TeknoBeek/KTS_Open_Source/Etiketler_PGN/001.png

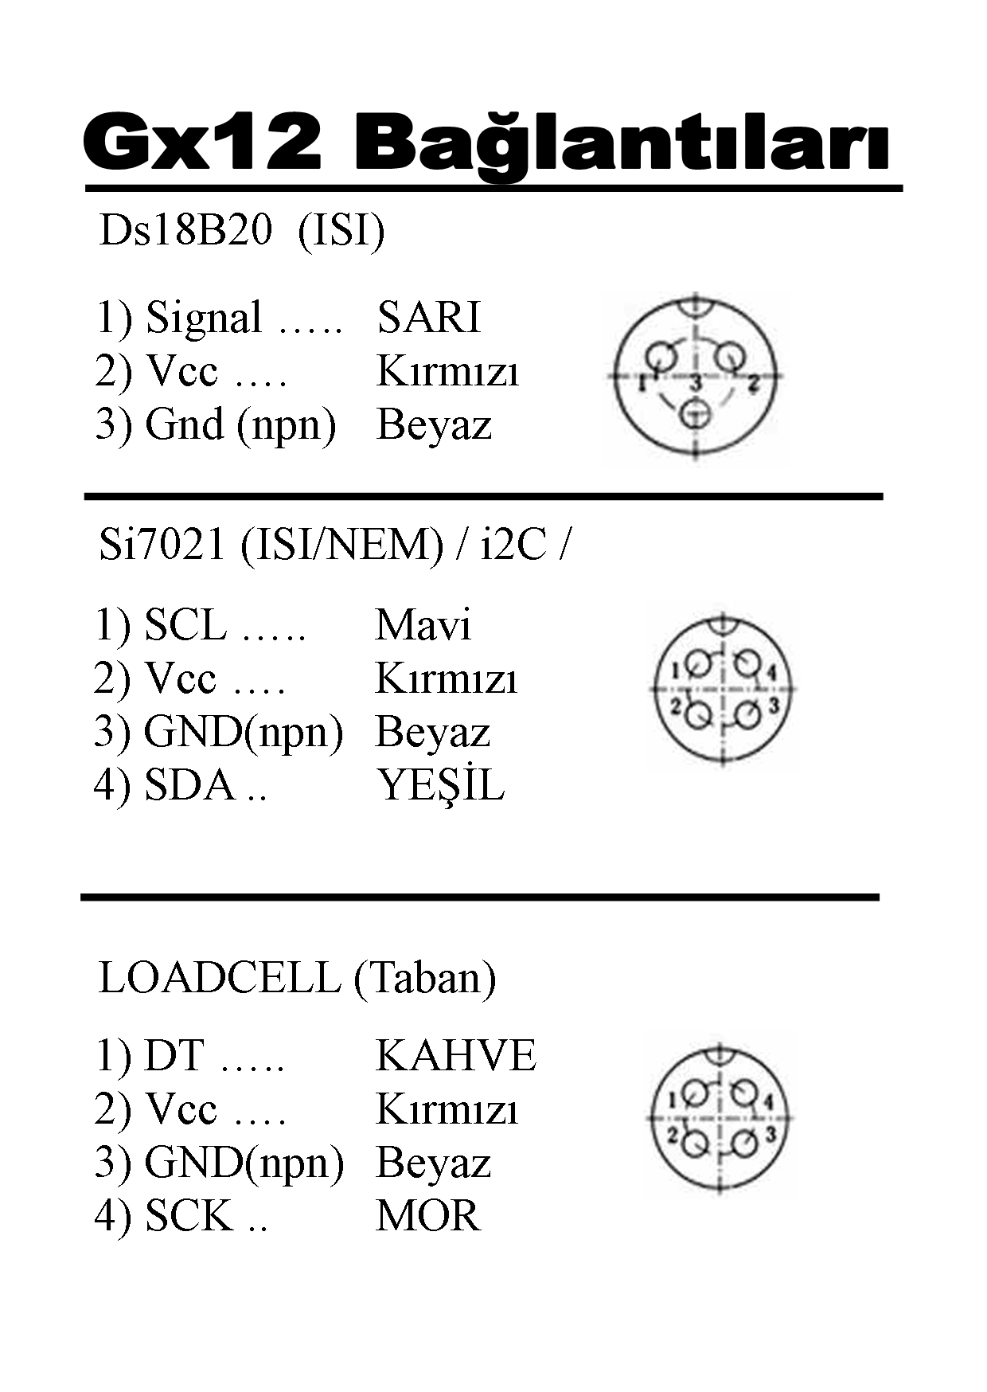
Etiketler_PGN/001.png
