TeknoBeek/KTS_Open_Source/Etiketler_PGN/002.png

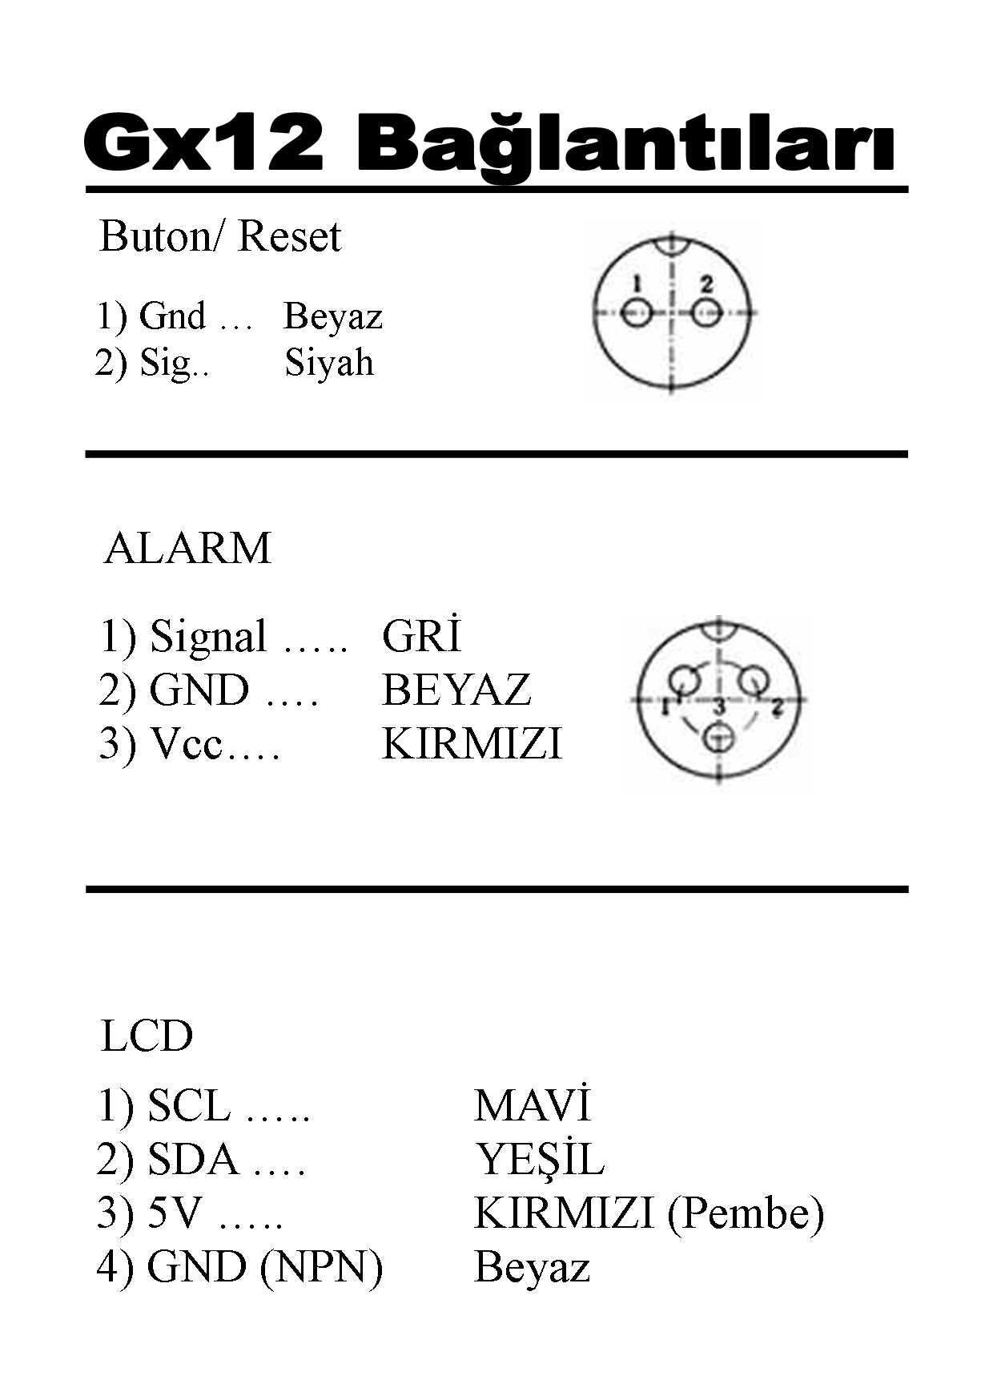
Etiketler_PGN/002.png
