TeknoBeek/KTS_Open_Source/Etiketler_PGN/003.png

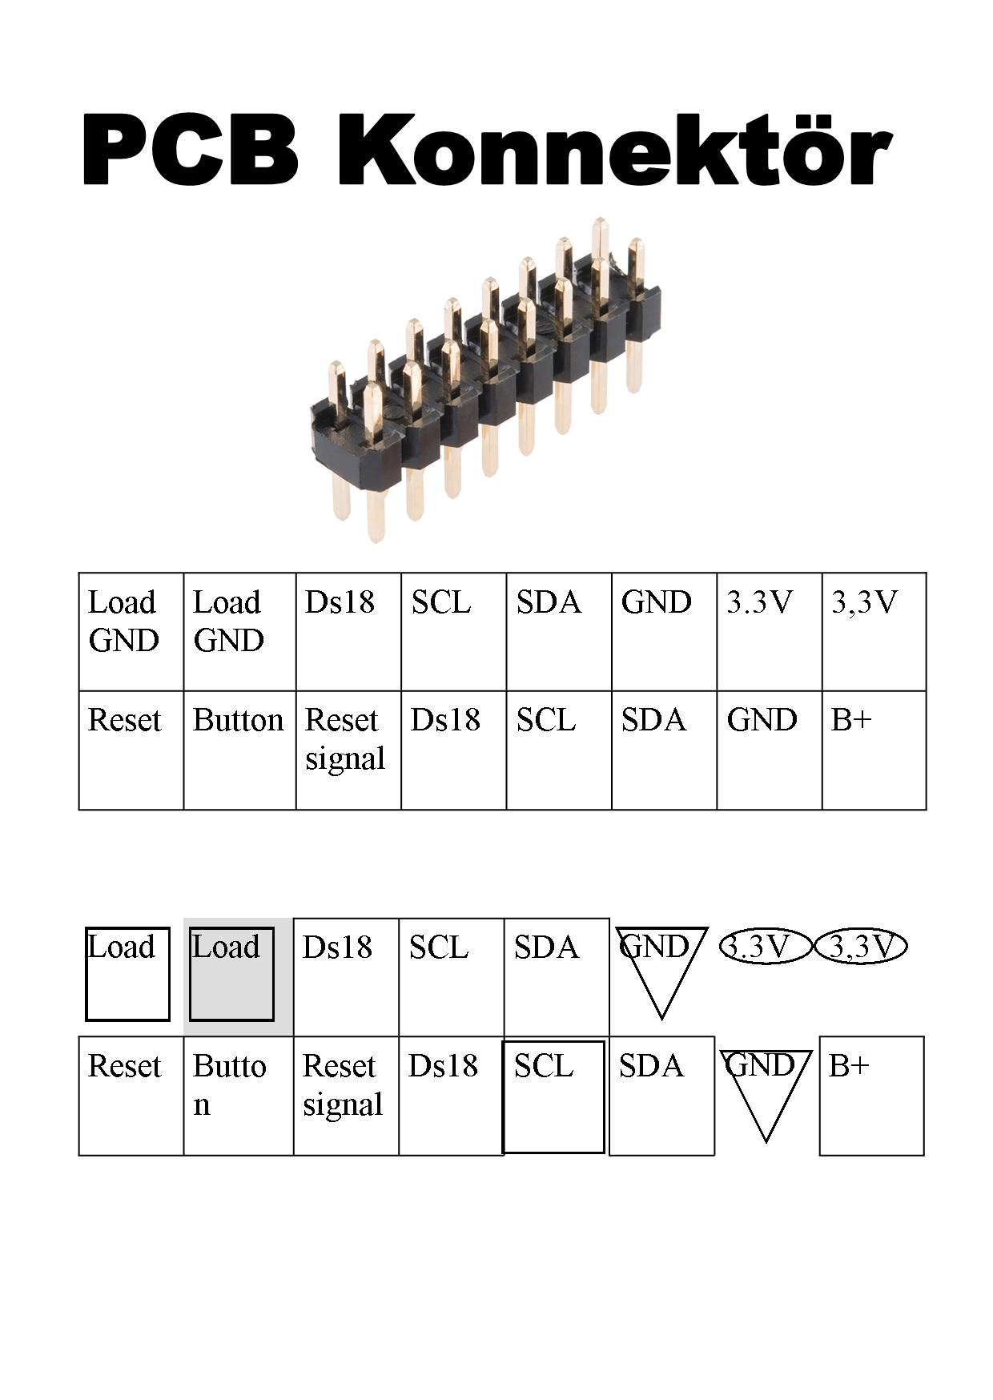
Etiketler_PGN/003.png
