TeknoBeek/KTS_Open_Source/Etiketler_PGN/004.png

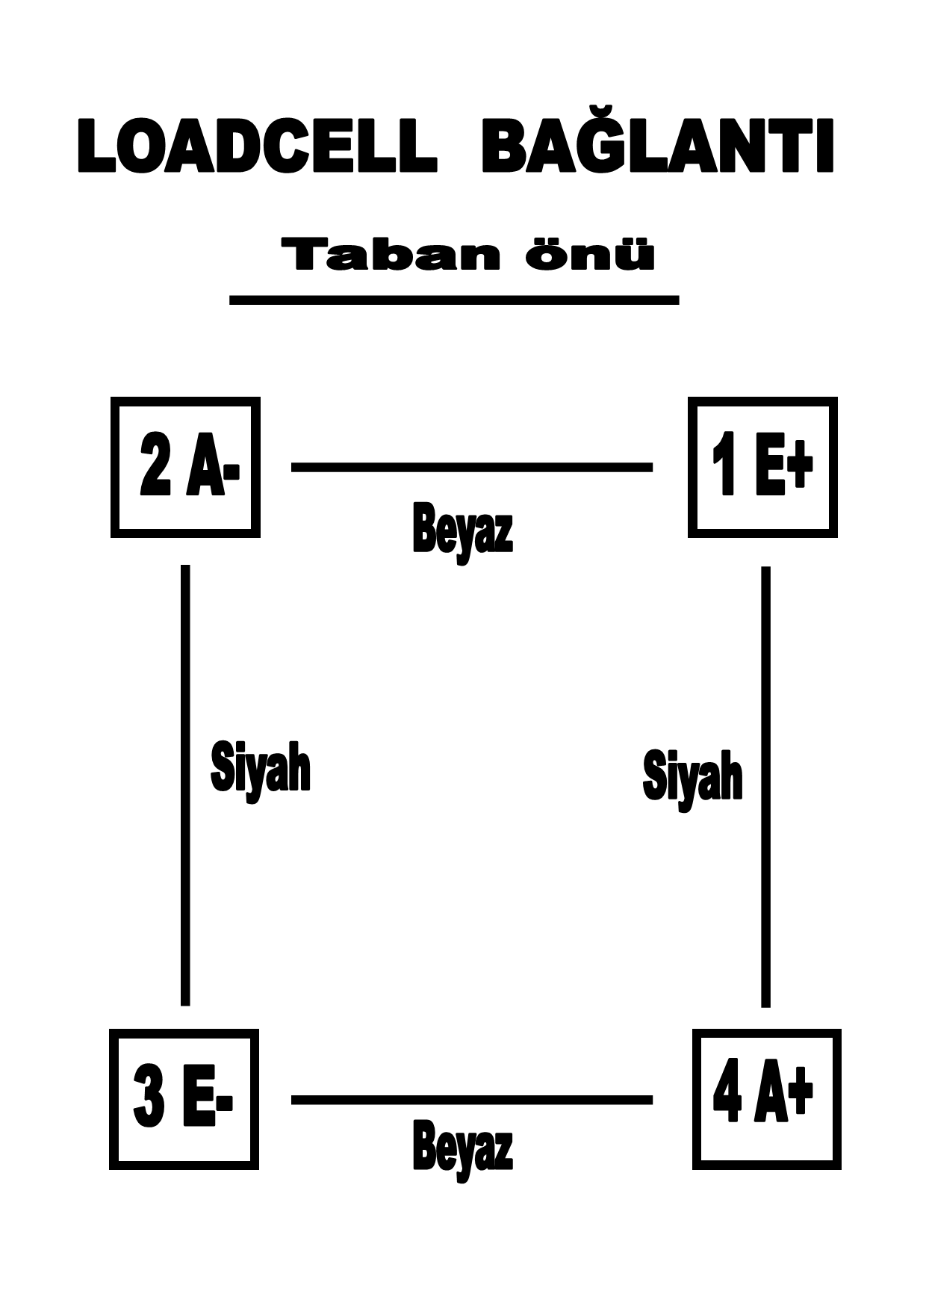
Etiketler_PGN/004.png
