TeknoBeek/KTS_Open_Source/Etiketler_PGN/005.png

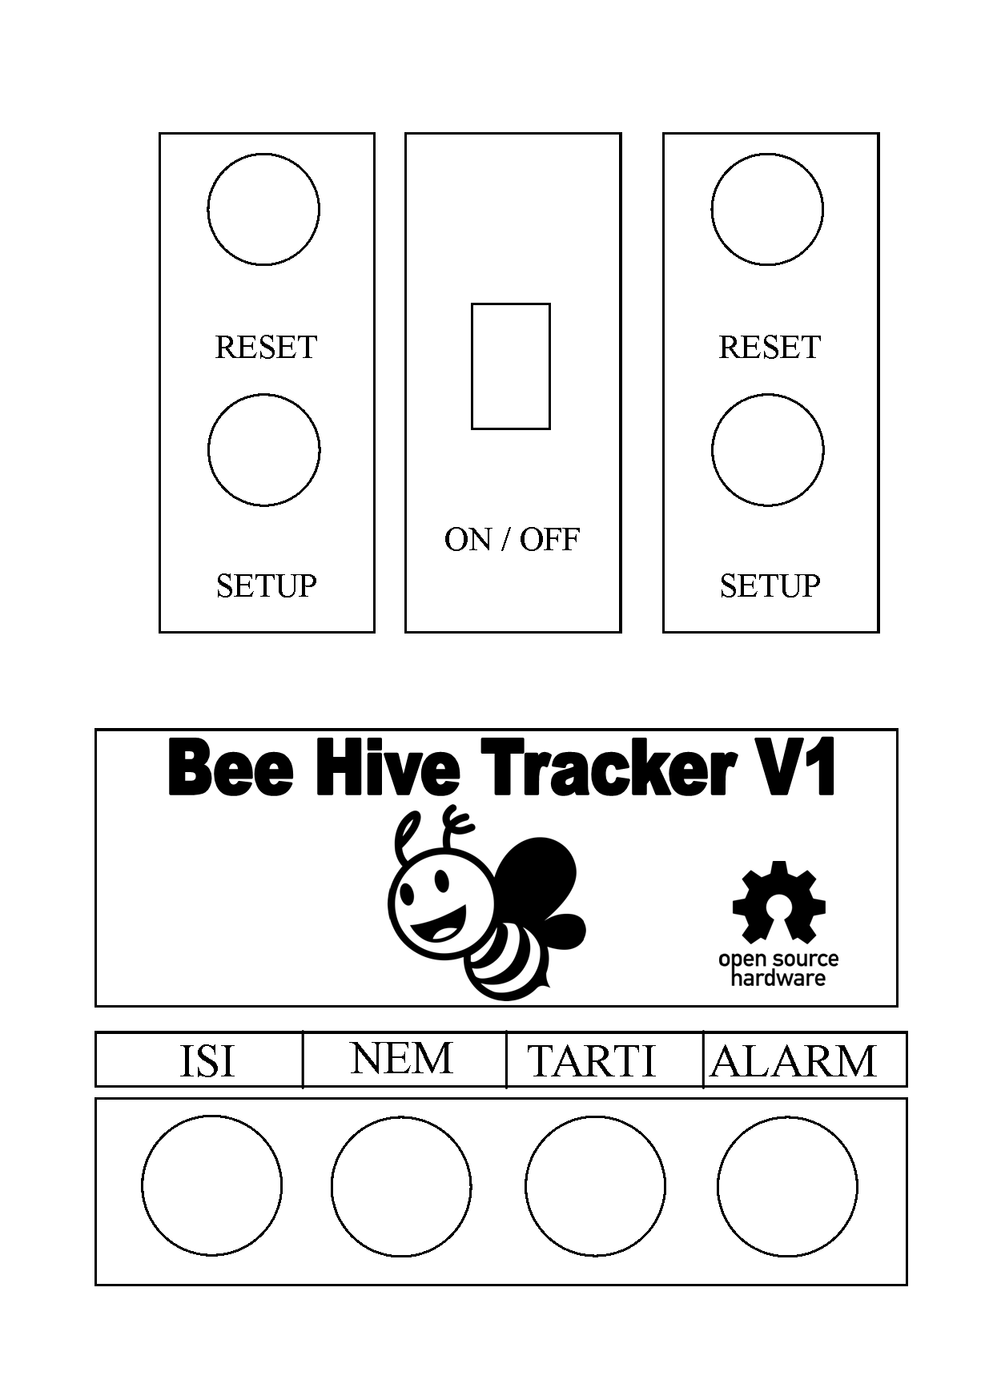
Etiketler_PGN/005.png
