TeknoBeek/KTS_Open_Source/Etiketler_PGN/006.png

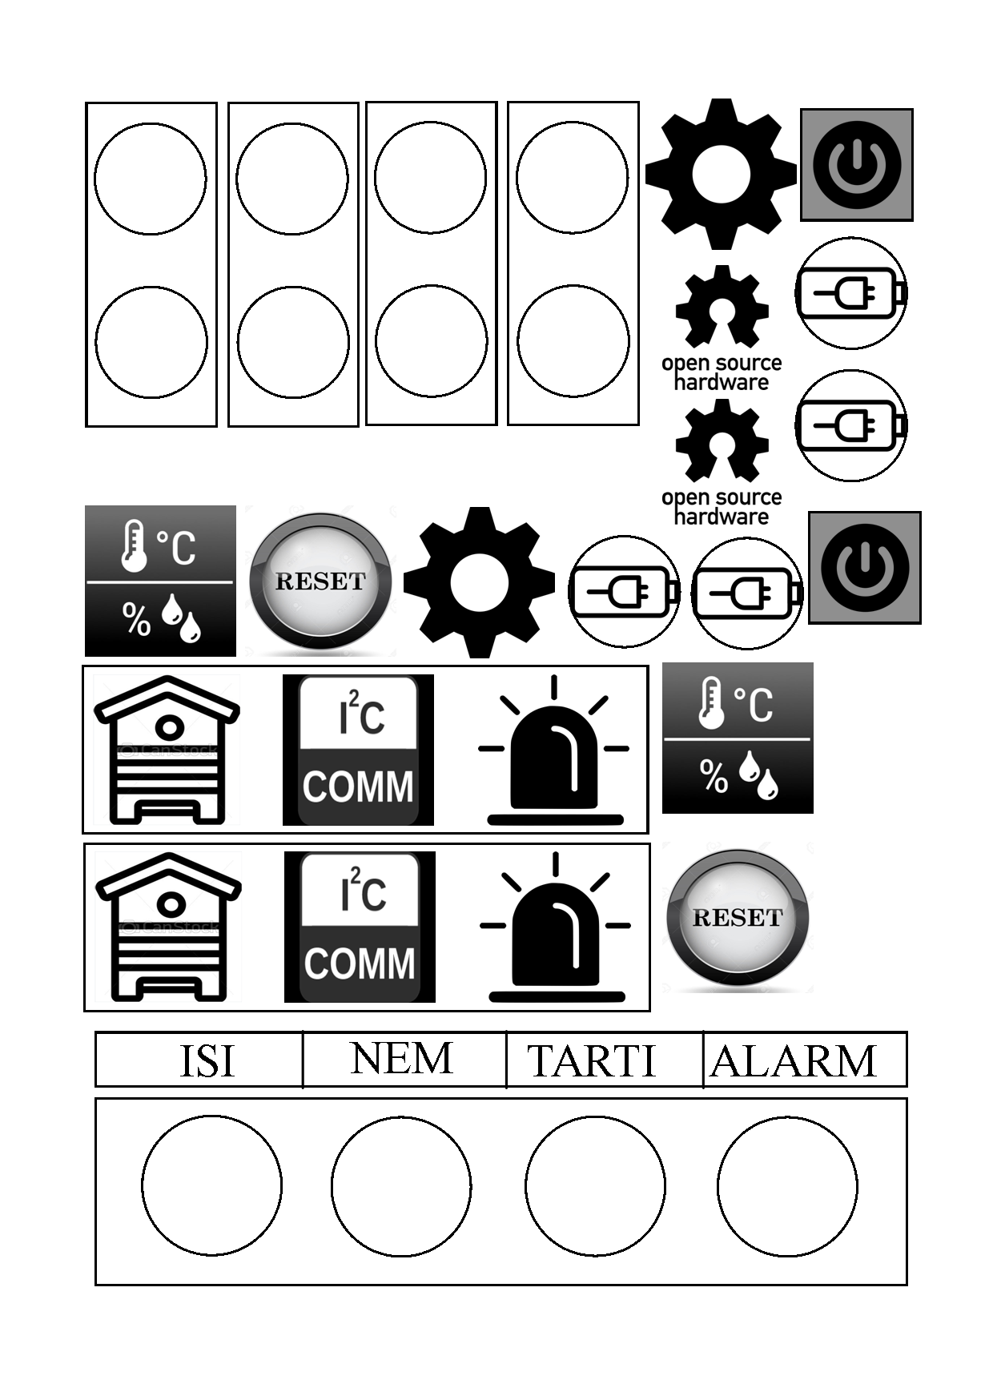
Etiketler_PGN/006.png
