TeknoBeek/KTS_Open_Source/Etiketler_PGN/007.png

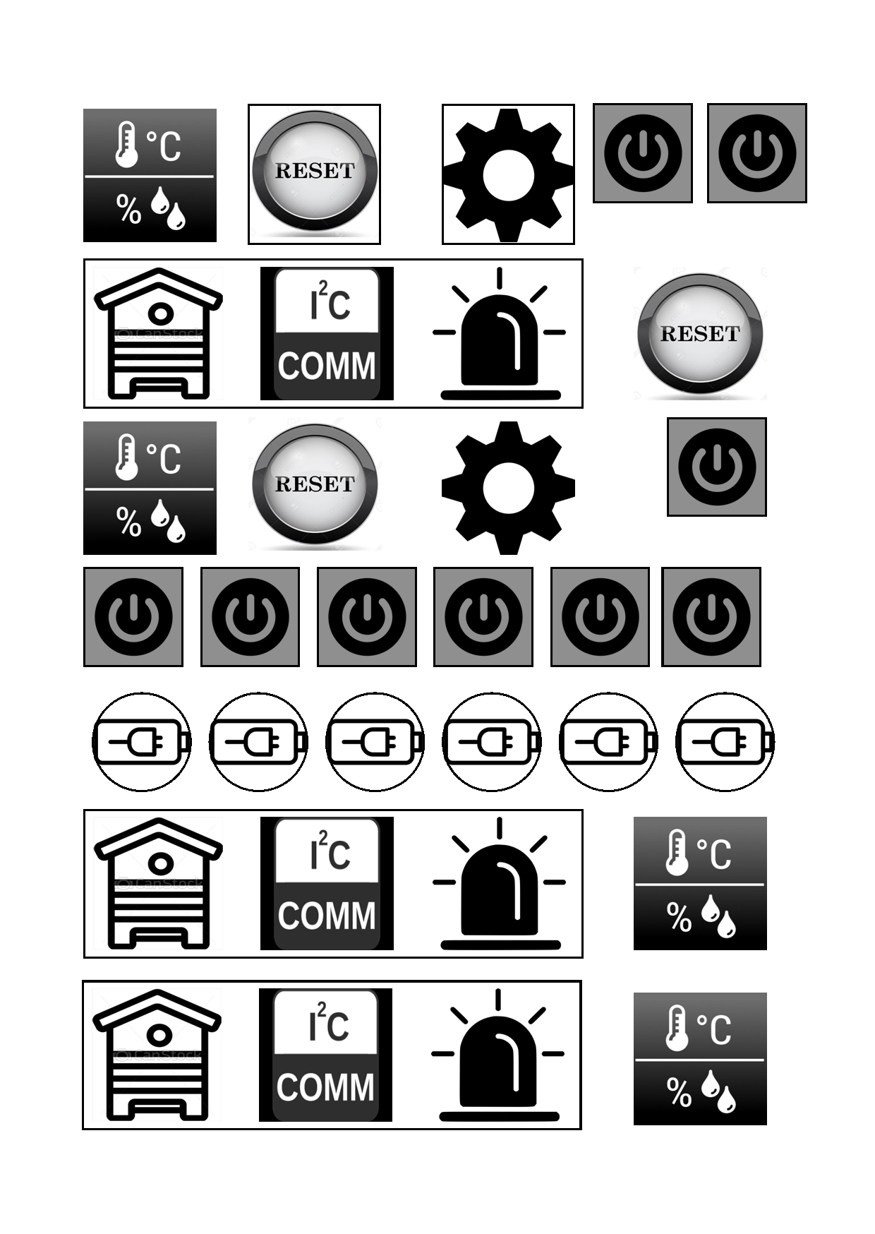
Etiketler_PGN/007.png
