TeknoBeek/KTS_Open_Source/Etiketler_PGN/008.png

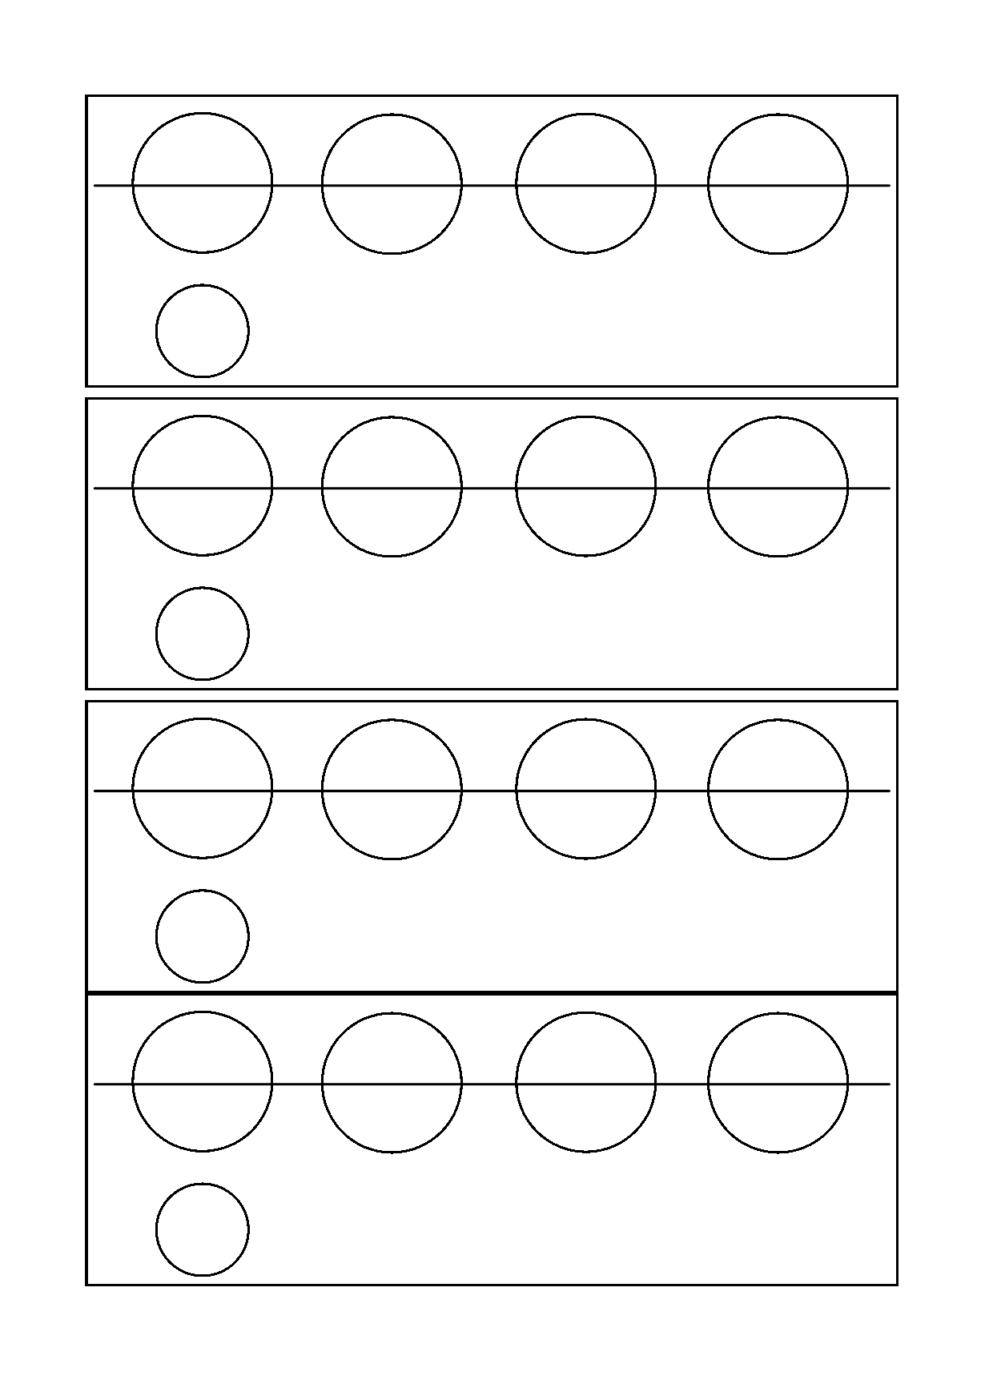
Etiketler_PGN/008.png
