TeknoBeek/KTS_Open_Source/Etiketler_PGN/009.png

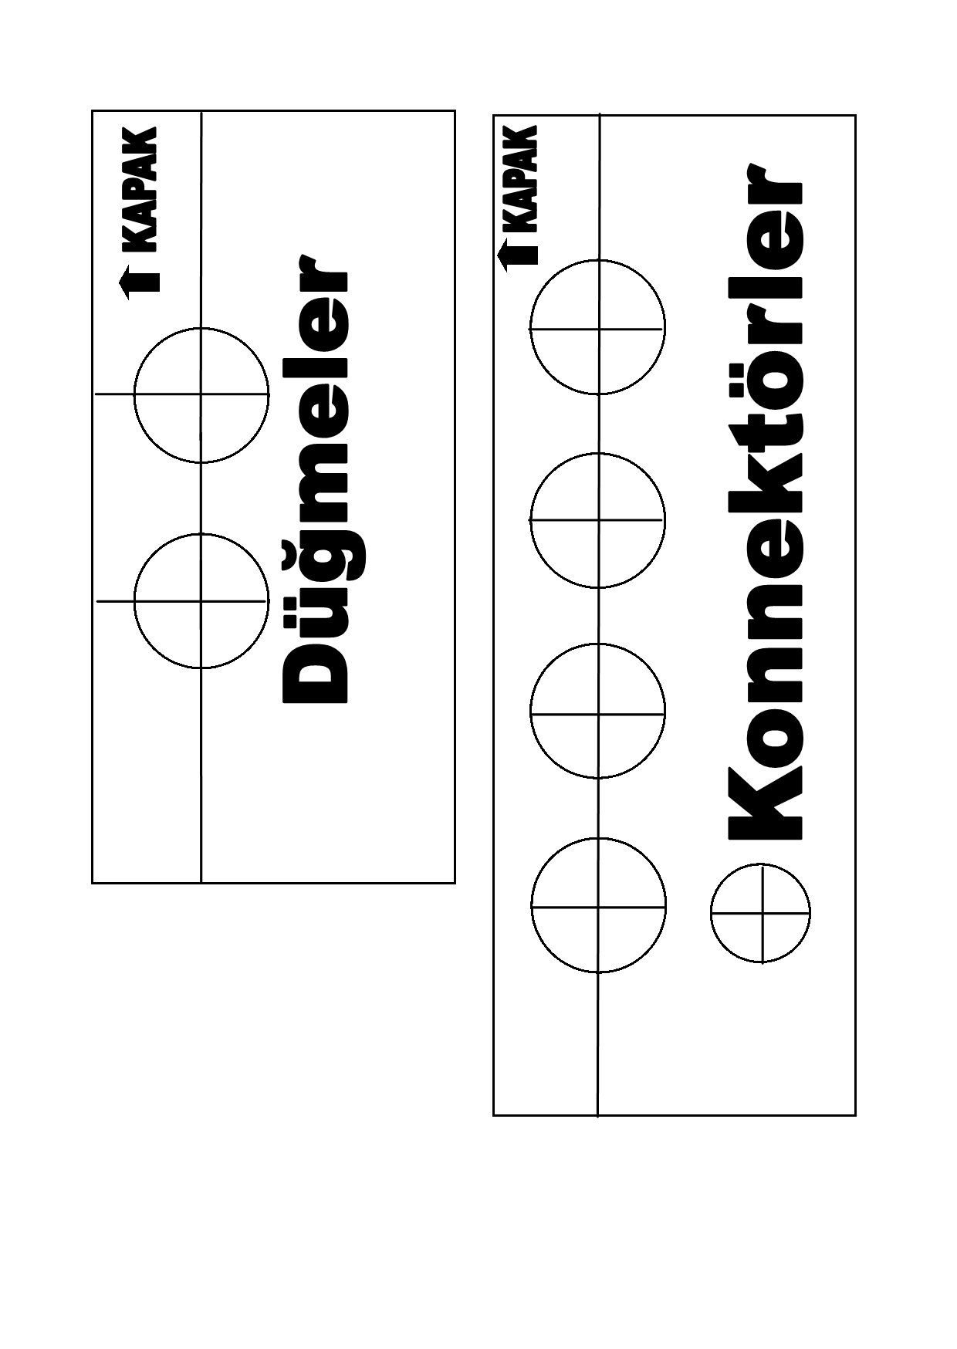
Etiketler_PGN/009.png
