TeknoBeek/KTS_Open_Source/Resimler/20210128_214419.jpg

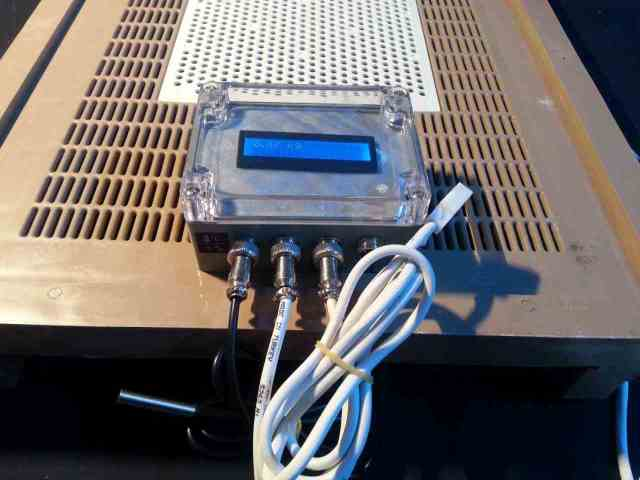
Resimler/20210128_214419.jpg
