TeknoBeek/KTS_Open_Source/Resimler/20210129_171541.jpg

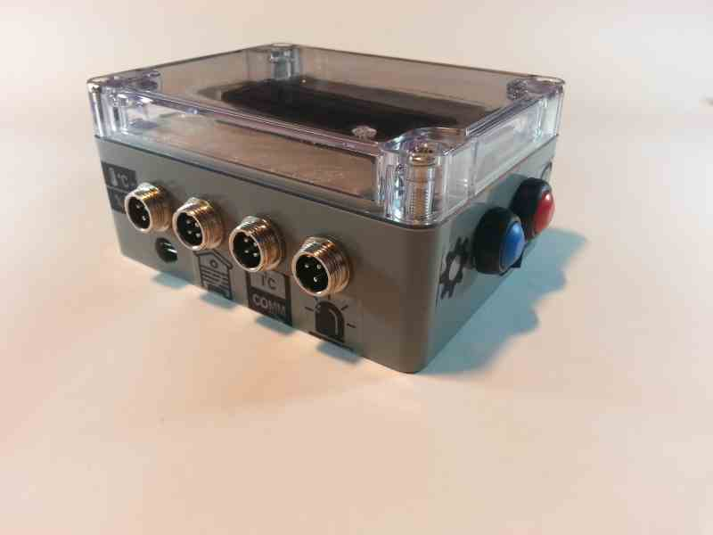
Resimler/20210129_171541.jpg
