TeknoBeek/KTS_Open_Source/Resimler/20210129_172927.jpg

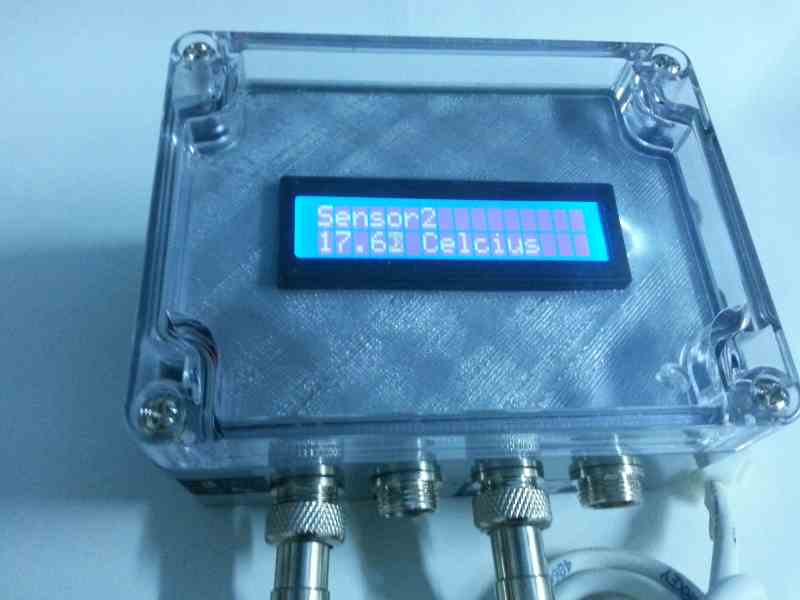
Resimler/20210129_172927.jpg
