TeknoBeek/KTS_Open_Source/Resimler/20210129_181911.jpg

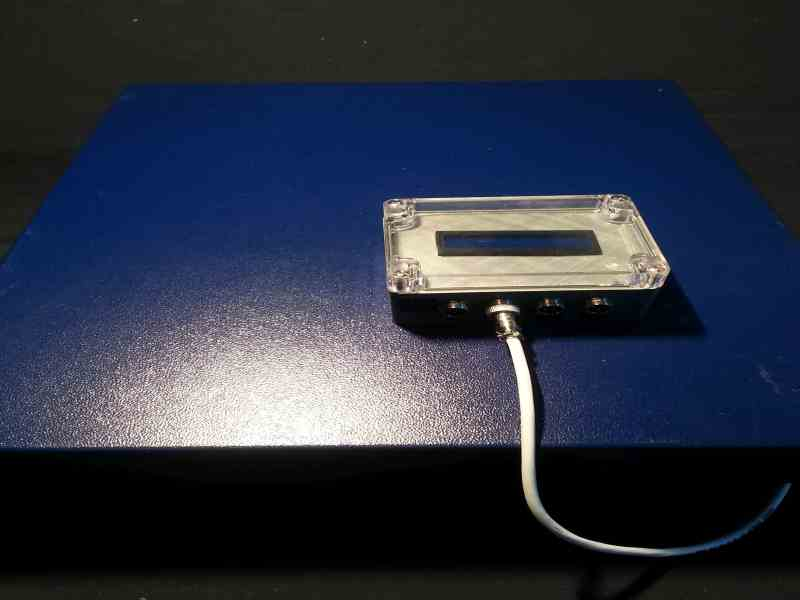
Resimler/20210129_181911.jpg
