TeknoBeek/KTS_Open_Source/Resimler/20210129_182238.jpg

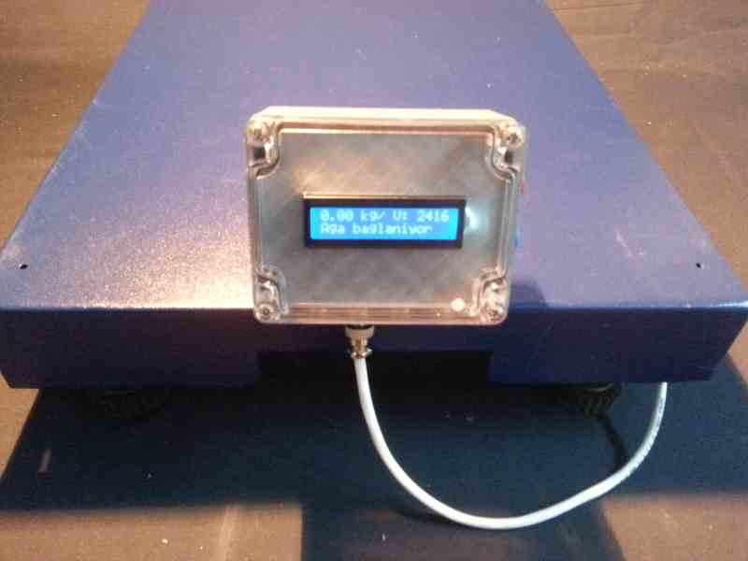
Resimler/20210129_182238.jpg
