TeknoBeek/KTS_Open_Source/Resimler/20210129_182449.jpg

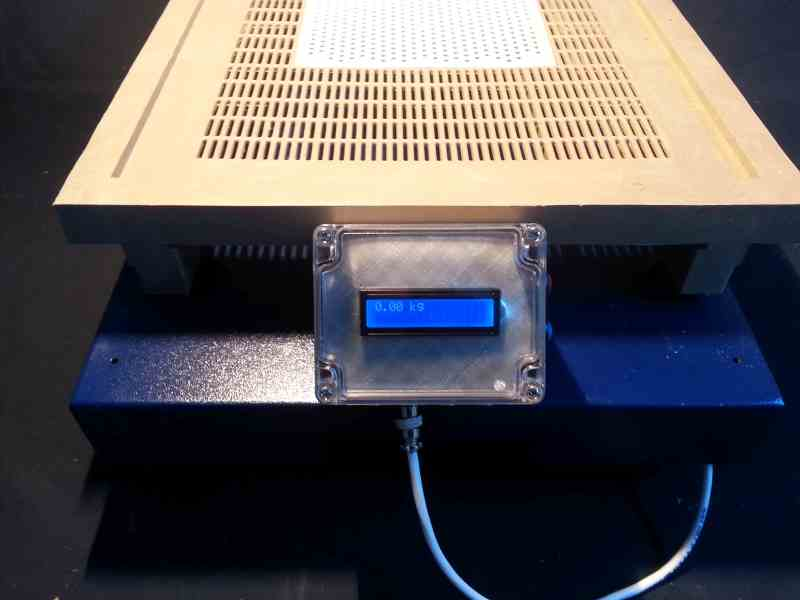
Resimler/20210129_182449.jpg
