TeknoBeek/KTS_Open_Source/Resimler/20210129_182549.jpg

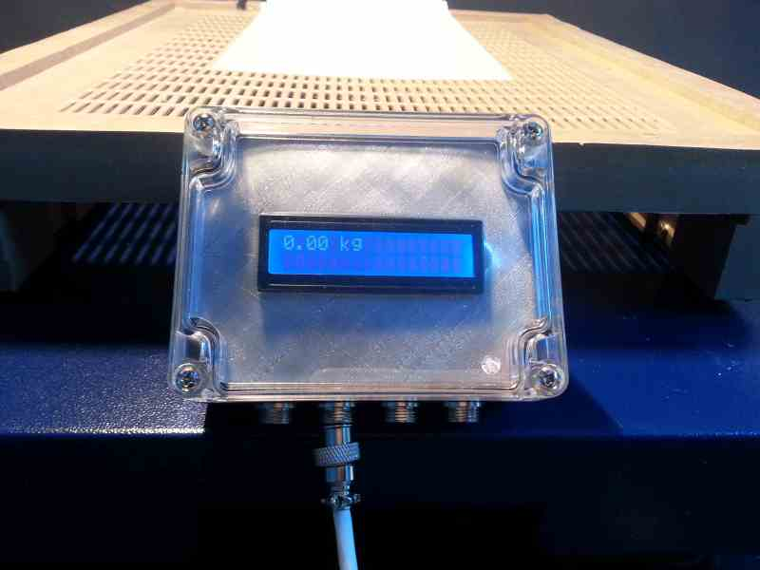
Resimler/20210129_182549.jpg
