TeknoBeek/KTS_Open_Source/Resimler/20211203_015421.jpg

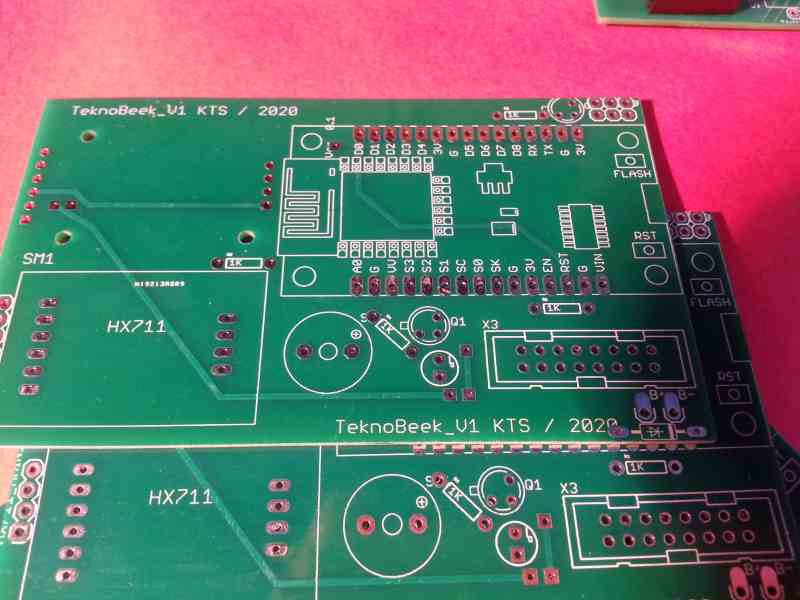
Resimler/20211203_015421.jpg
