TeknoBeek/KTS_Open_Source/Resimler/20211203_015532(0).jpg

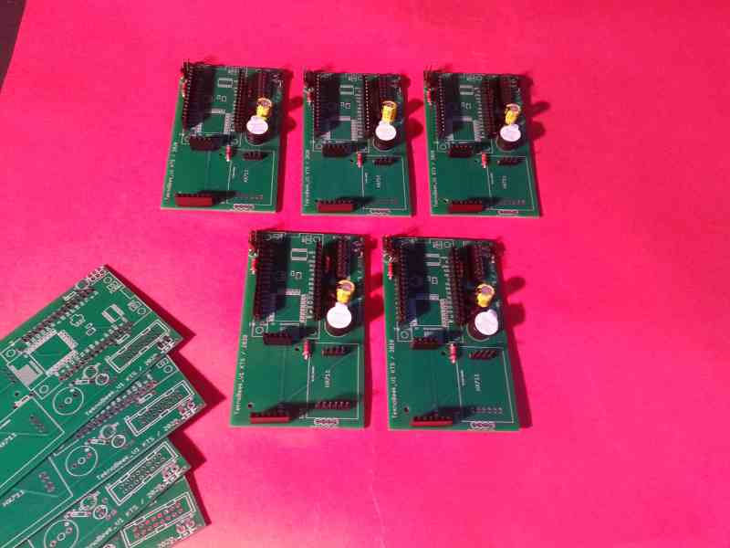
Resimler/20211203_015532(0).jpg
