TeknoBeek/KTS_Open_Source/Resimler/20211203_015712.jpg

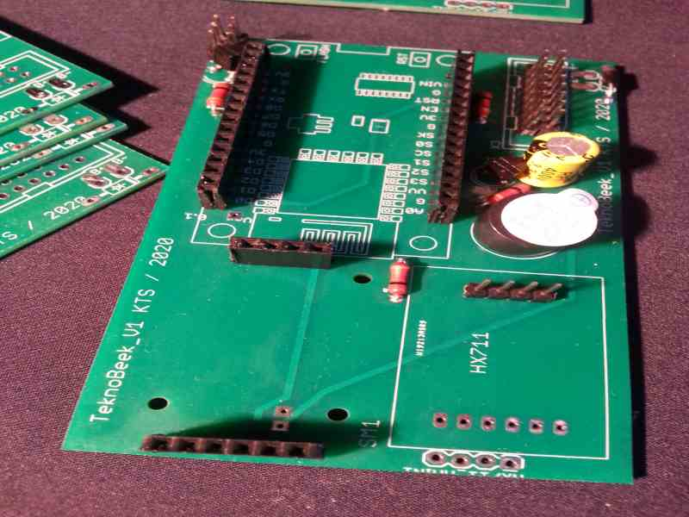
Resimler/20211203_015712.jpg
