TeknoBeek/KTS_Open_Source/Resimler/20211203_021402.jpg

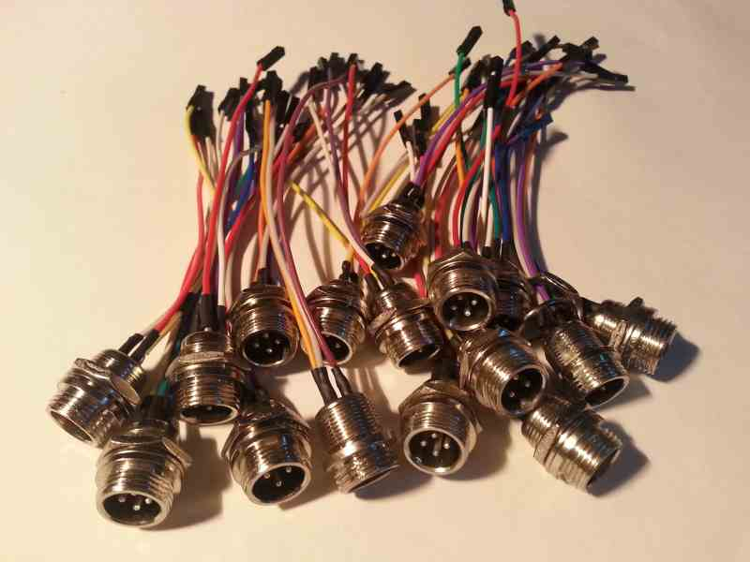
Resimler/20211203_021402.jpg
