TeknoBeek/KTS_Open_Source/Resimler/20211203_021422.jpg

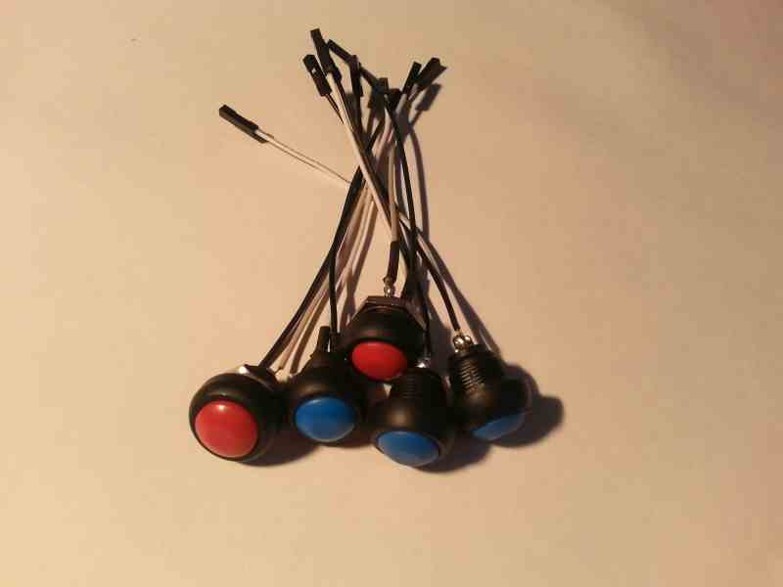
Resimler/20211203_021422.jpg
