TeknoBeek/KTS_Open_Source/Resimler/20211203_021454.jpg

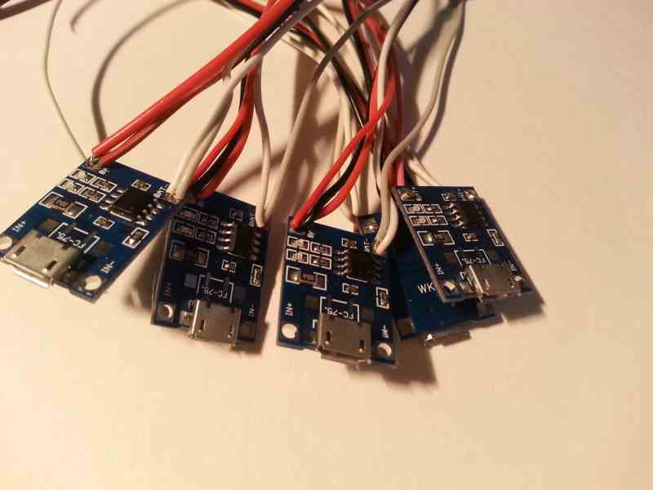
Resimler/20211203_021454.jpg
