TeknoBeek/KTS_Open_Source/Resimler/20211203_021526.jpg

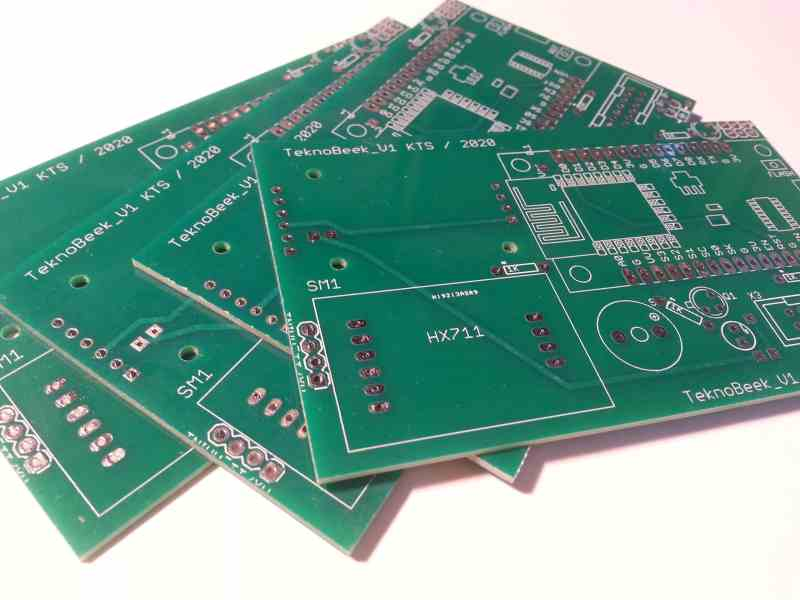
Resimler/20211203_021526.jpg
