TeknoBeek/KTS_Open_Source/Resimler/20211203_021615.jpg

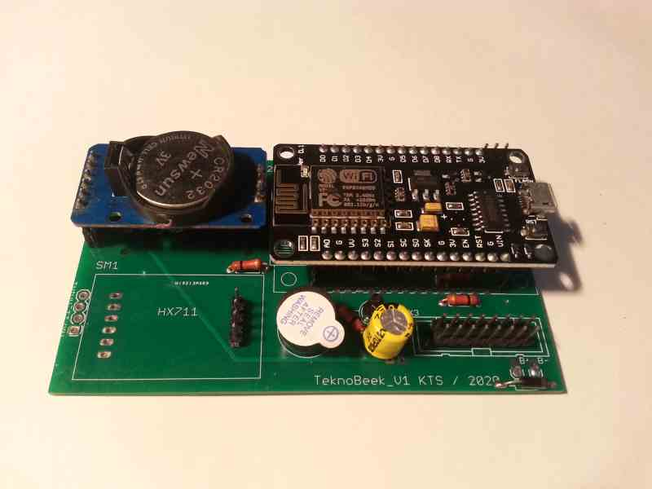
Resimler/20211203_021615.jpg
