TeknoBeek/KTS_Open_Source/Resimler/20211203_024931.jpg

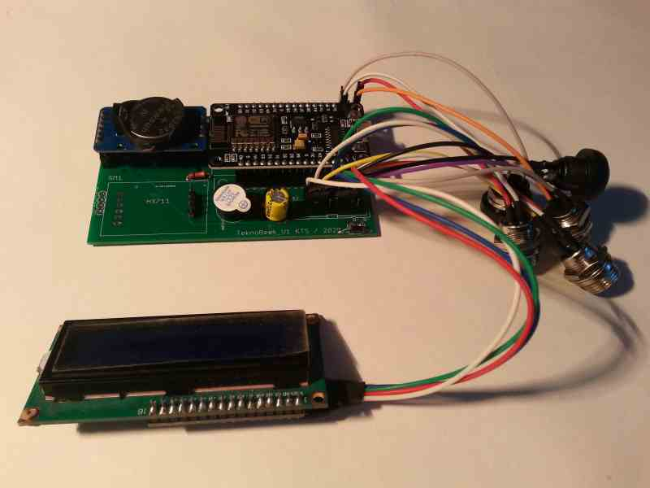
Resimler/20211203_024931.jpg
