TeknoBeek/KTS_Open_Source/Resimler/20211203_025152.jpg

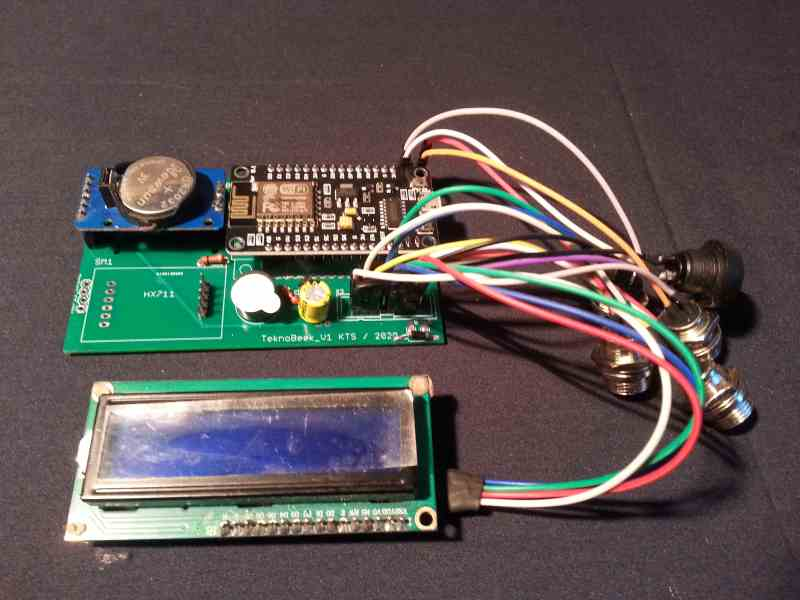
Resimler/20211203_025152.jpg
