TeknoBeek/KTS_Open_Source/Resimler/SAM_7676.jpg

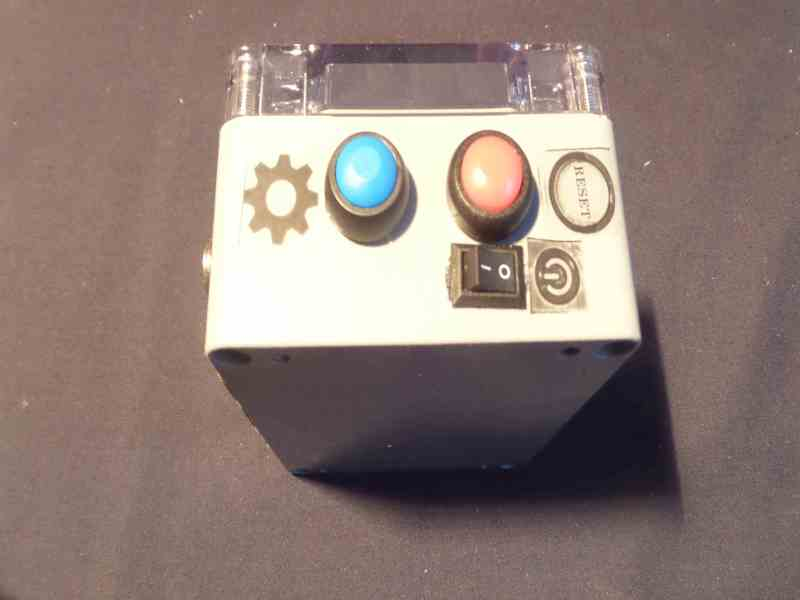
Resimler/SAM_7676.jpg
