TeknoBeek/KTS_Open_Source/Resimler/SAM_7705.jpg

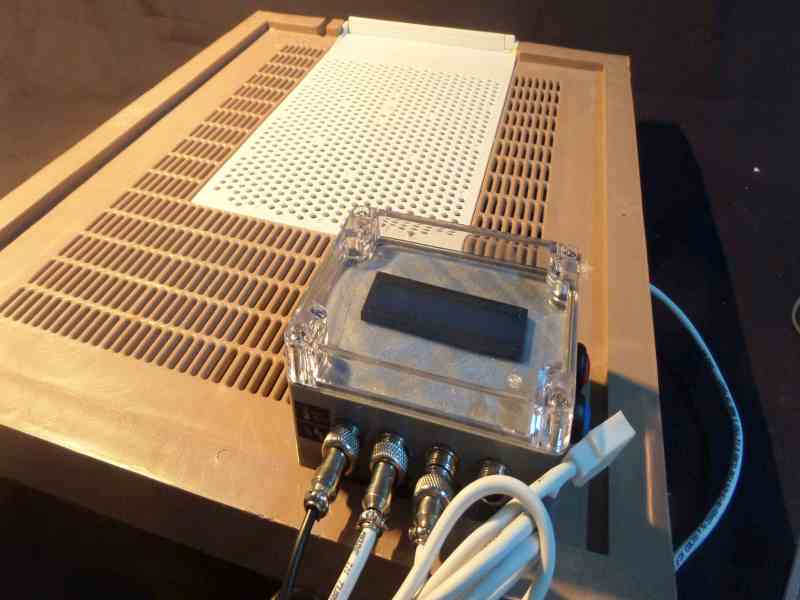
Resimler/SAM_7705.jpg
