TeknoBeek/KTS_Open_Source/Resimler/SAM_7712.JPG

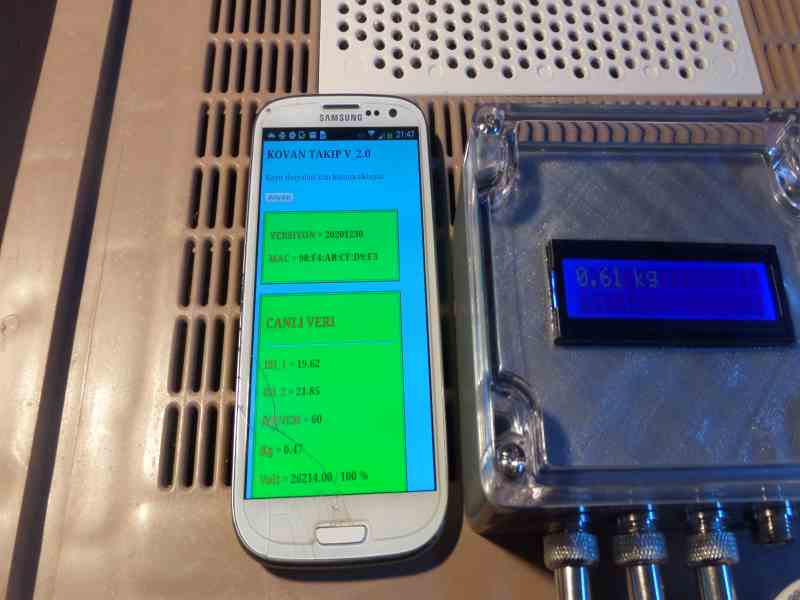
Resimler/SAM_7712.JPG
