TeknoBeek/KTS_Open_Source/Resimler/SAM_7713.jpg

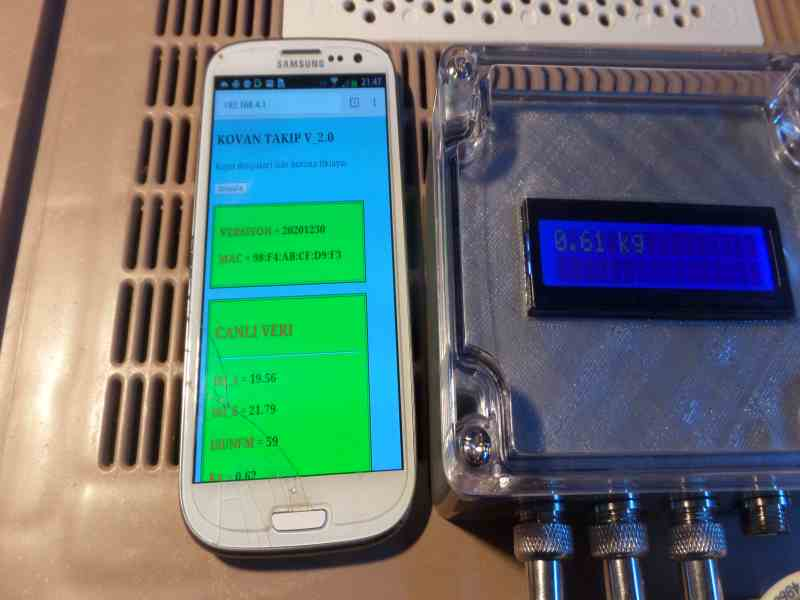
Resimler/SAM_7713.jpg
