TeknoBeek/KTS_Open_Source/Resimler/taban_002.jpg

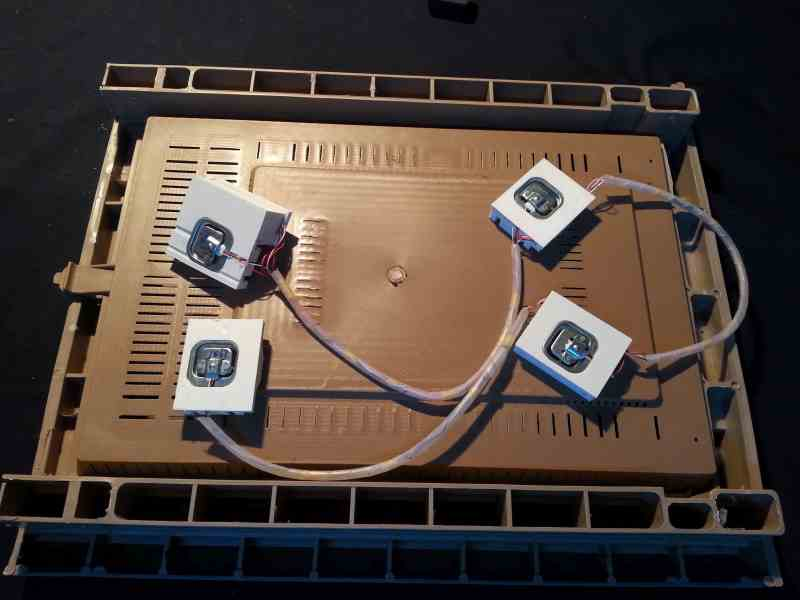
Resimler/taban_002.jpg
