TeknoBeek/KTS_Open_Source/Resimler/Things001.jpg

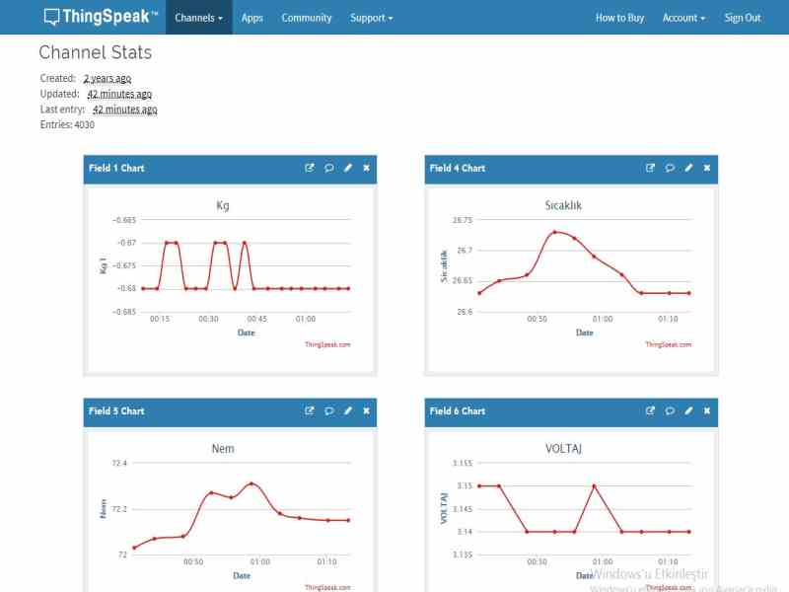
Resimler/Things001.jpg
