TeknoBeek/KTS_Open_Source/Resimler/Things002.jpg

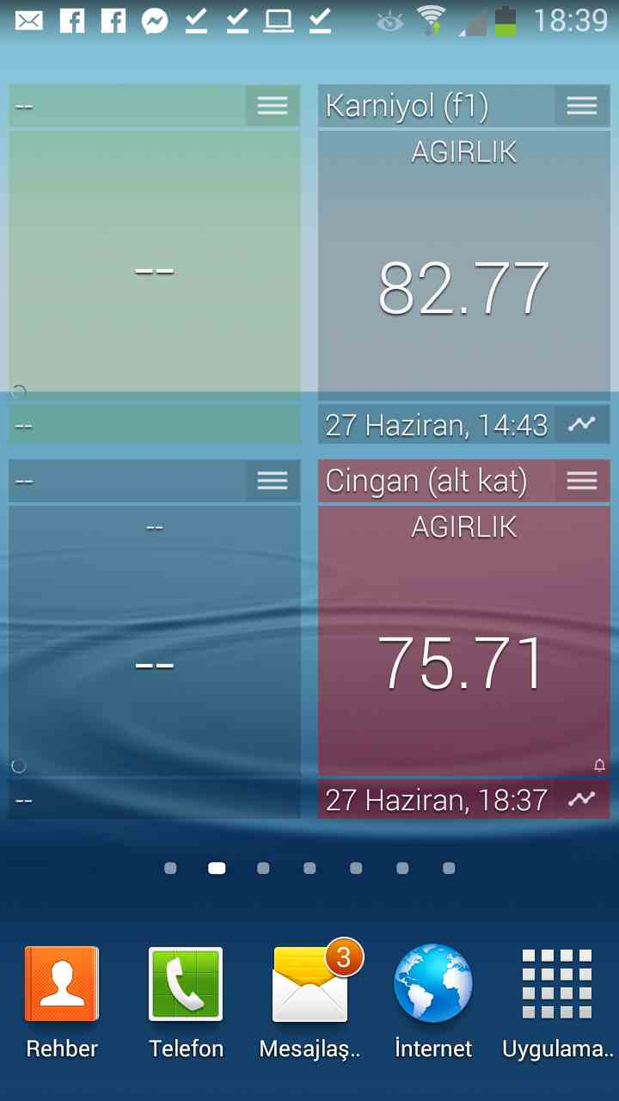
Resimler/Things002.jpg
